aditya23043/split36/src/firmware/kmk_firmware-main/boards/rhymestone/README.md

# Rhymestone

rhymestone

The Rhymestone is 40-key ortholinear split keyboard. Originally the Rhymestone
was created to be sold alongside the Treadstone and used as either a Macro pad
or a 10-key numpad, hence the similar naming conventions. However; the
Rhymestone is also often used as a standalone split keyboard by people who
prefer a 5 column ortholinear layout.

Extensions enabled by default  
- [Layers](/docs/en/layers.md) Need more keys than switches? Use layers.
- [BLE_Split](/docs/en/split_keyboards.md) Connects halves without wires
- [HoldTap](/docs/en/holdtap.md) Allows mod keys to act as different keys when tapped.

Common Extensions
- [Split](/docs/en/split_keyboards.md) Connects halves using a wire
- [Power](/docs/en/power.md) Powersaving features for battery life

## Microcontroller support

Update this line in `kb.py` to any supported microcontroller in `kmk/quickpin/pro_micro`:

```python
from kmk.quickpin.pro_micro.boardsource_blok import pinout as pins
```
