aditya23043/split36/src/firmware/kmk_firmware-main/boards/zodiark/README.md

# Zodiark

Zodiark

A split keyboard with 5x7 including a thumb cluster, encoders on each side, per
key RGB, and 2x I2C headers per side, supporting 1.3"/.96" 128x64 OLEDs (the
1.3" is an SSH1106 OLED, .91" 128x32 OLEDs.

Hardware Availability: Pending Group Buy - [Discord Link](https://discord.gg/BCSbXwskVt)

Extensions enabled by default  
- [Split](/docs/split.md) Connects halves using a wire.
- [Layers](/docs/layers.md) Need more keys than switches? Use layers.
- [PEG_RGB](/docs/peg_rgb_matrix.md) Light it up!
- [Display](/docs/en/display.md) Show information on the mini OLED display
