aditya23043/split36/src/firmware/kmk_firmware-main/boards/boardsource/Lulu/README.md

# Lulu

Lulu

Based on the form factor of the Lily58, but with new features. The Lulu is a 58 key split keyboard design by Boardsource, featuring a 6x4 columnar stagger and 4 thumb cluster keys on each hand. The Lulu is a perfect choice for people who want to be on a split keyboard but still want to have a fairly standard amount of keys, and a premium case available.

Hardware Availability: [PCB & Case Source](https://boardsource.xyz/store/5ec9df84c6b834480de6c3d0)  
kb.py is designed to work with the PCBA version directly from them.

Extensions enabled by default  
- [Split](/docs/en/split.md) Connects halves using a wire.
- [Layers](/docs/en/layers.md) Need more keys than switches? Use layers.
- [PEG_RGB](/docs/en/peg_rgb_matrix.md) Light it up!
- [Display](/docs/en/display.md) Show information on the mini OLED display

Common Extensions
- [Power](/docs/en/power.md) Powersaving features for battery life.
- [BLE_Split](/docs/en/split.md) Connects halves without wires (For the DIY version)
