aditya23043/split36/src/firmware/kmk_firmware-main/boards/boardsource/microdox/README.md

# Microdox

microdox

The Microdox is is a feature-packed 30% split columnar staggered keyboard. Even
though the Microdox is an extremely small keyboard it offers tons of features
from larger boards while maintaining a tiny footprint.

Extensions enabled by default  
- [Layers](/docs/en/layers.md) Need more keys than switches? Use layers.
- [BLE_Split](/docs/en/split_keyboards.md) Connects halves without wires
- [HoldTap](/docs/en/holdtap.md) Allows mod keys to act as different keys when tapped.

Common Extensions
- [Split](/docs/en/split_keyboards.md) Connects halves using a wire
- [Power](/docs/enpower.md) Powersaving features for battery life

## Microcontroller support

Update this line in `kb.py` to any supported microcontroller in `kmk/quickpin/pro_micro`:

```python
from kmk.quickpin.pro_micro.boardsource_blok import pinout as pins
```
