aditya23043/split36/src/firmware/kmk_firmware-main/boards/gtips/reviung39/README.md

# Reviung39

Reviung39

Reviung39 is a 39 key keyboard designed by gtips. The Reviung39 sits somewhere
between an Atreus and a Corne, you get some nice ergonomic benefits based on its
quasi-split design and since a true split keyboard isn't for everyone, this is
an awesome middle ground. I find this keyboard extremely comfortable to use.

kb.py is designed to work with the nice!nano

Hardware Availability: [PCB & Case Data](https://github.com/gtips/reviung)

Extensions enabled by default
- [Layers](/docs/en/layers.md) Need more keys than switches? Use layers.
- [RGB](/docs/en/rgb.md) Light it up
- [HoldTap](/docs/en/holdtap.md) Allows mod keys to act as different keys when tapped.

## Microcontroller support

Update this line in `kb.py` to any supported microcontroller in `kmk/quickpin/pro_micro`:

```python
from kmk.quickpin.pro_micro.boardsource_blok import pinout as pins
```
