aditya23043/split36/imgs/2025-02-08_02-30.png

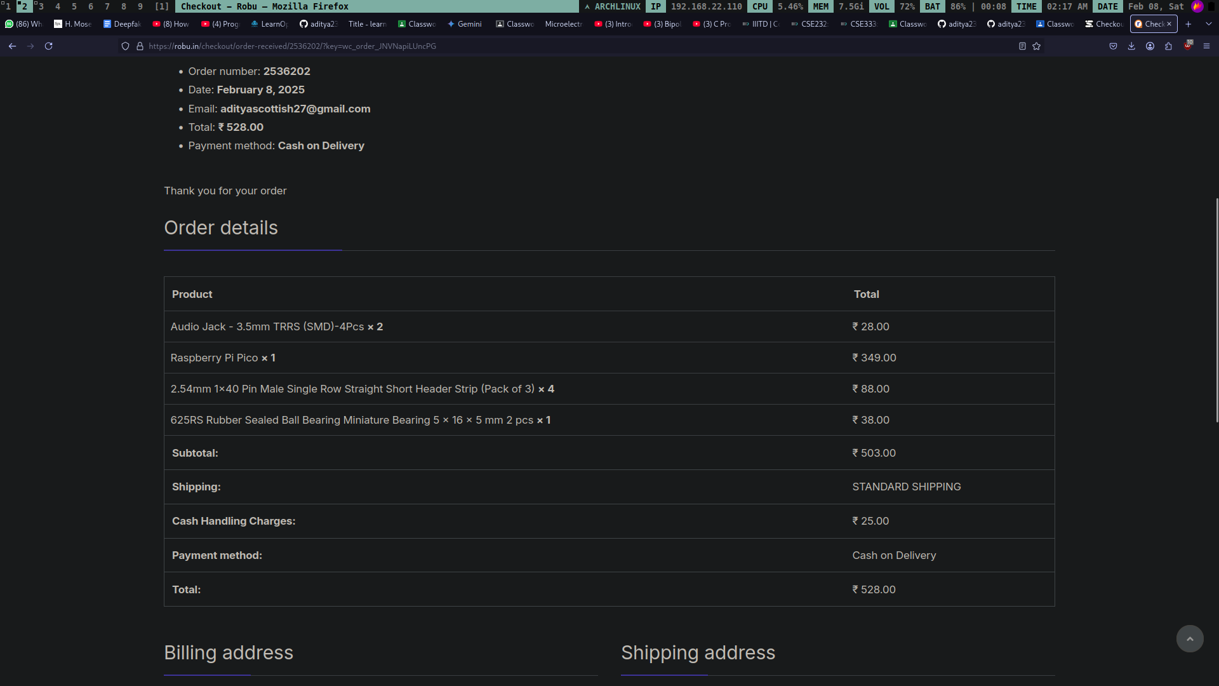
imgs/2025-02-08_02-30.png
