aditya23043/split36/imgs/2025-02-08_02-30_1.png

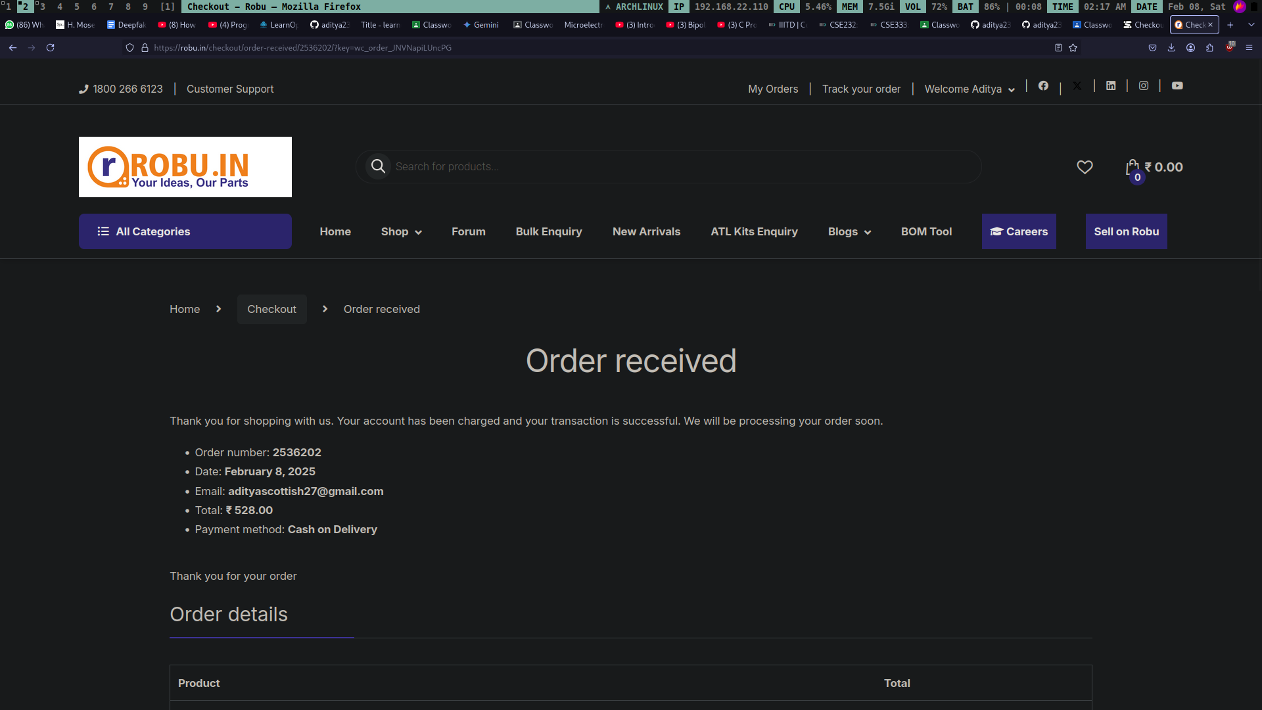
imgs/2025-02-08_02-30_1.png
