aditya23043/split36/imgs/2025-03-31_17-45.png

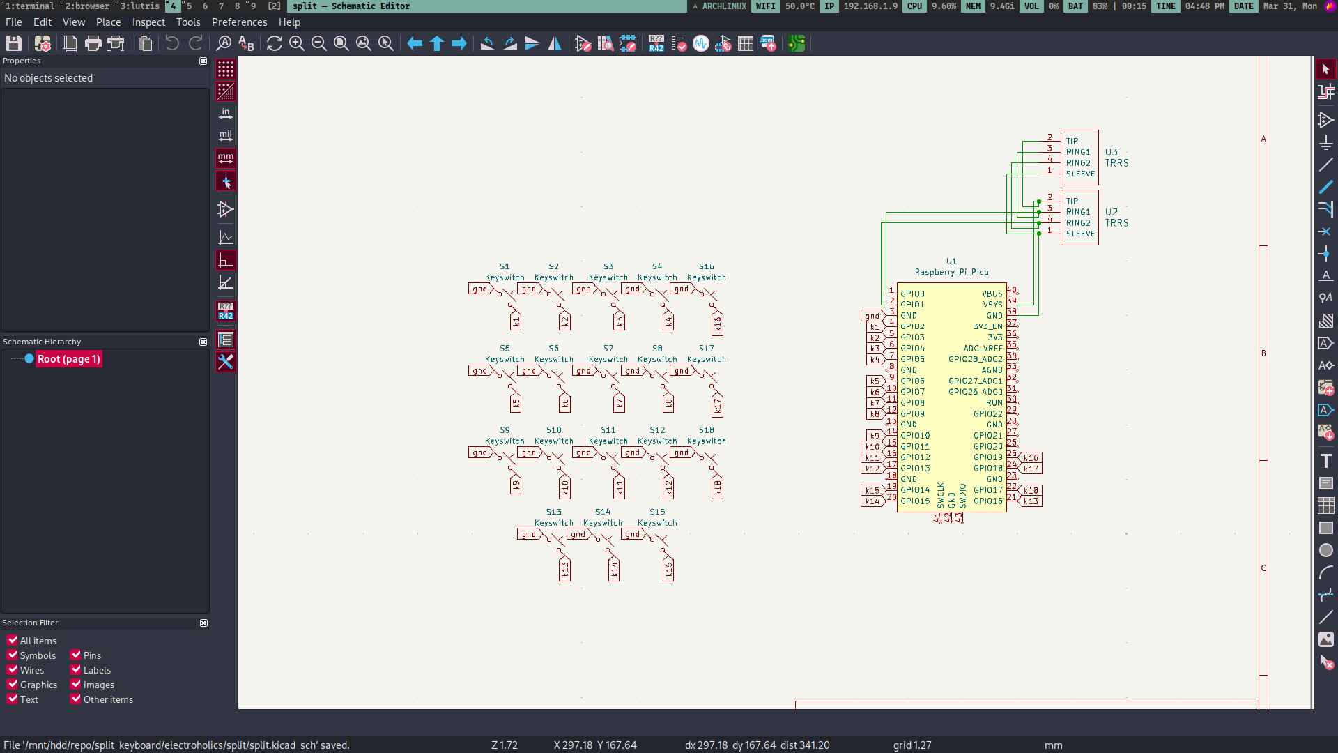
imgs/2025-03-31_17-45.png
