aditya23043/split36/imgs/2025-04-11_23-26.png

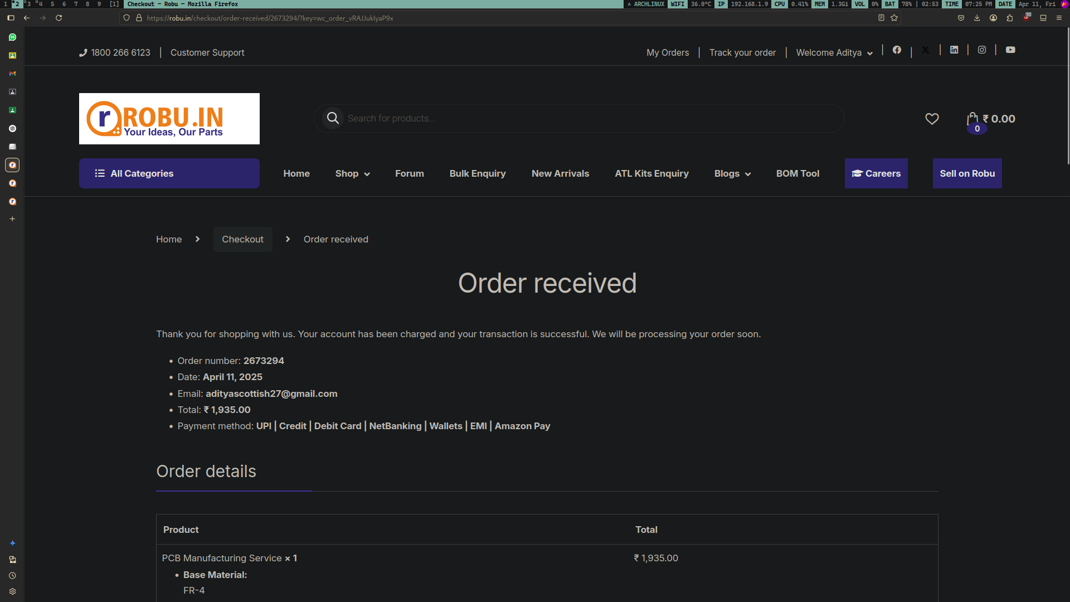
imgs/2025-04-11_23-26.png
