aditya23043/split36/imgs/dslr/IMG_3497.JPG

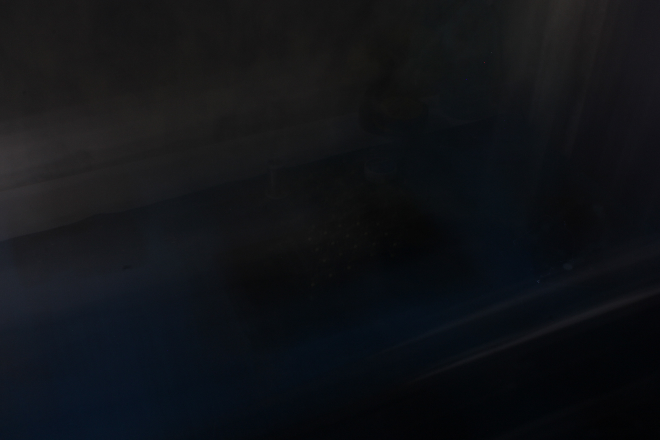
imgs/dslr/IMG_3497.JPG
