aditya23043/split36/imgs/dslr/IMG_3498.JPG

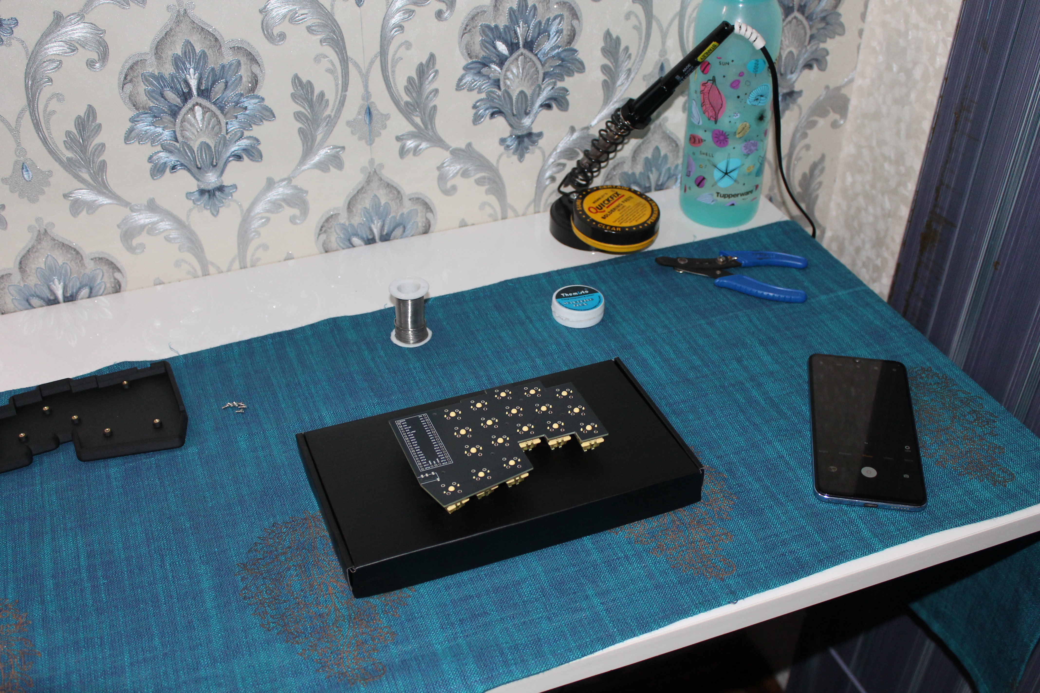
imgs/dslr/IMG_3498.JPG
