aditya23043/split36/imgs/dslr/IMG_3500.JPG

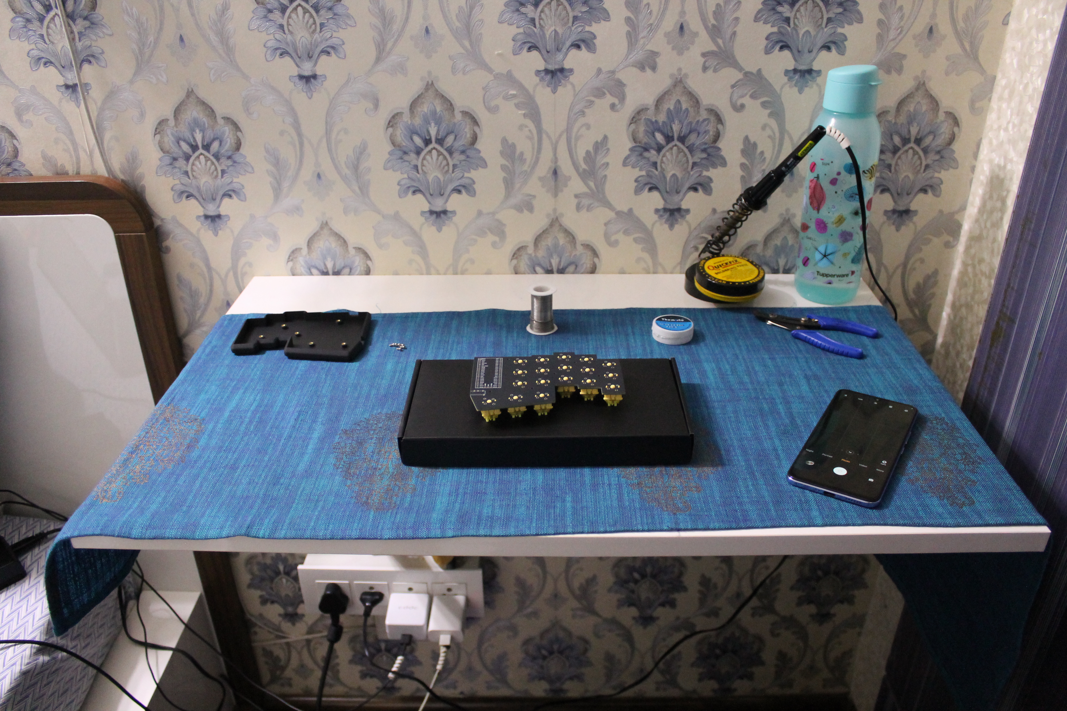
imgs/dslr/IMG_3500.JPG
