aditya23043/split36/imgs/dslr/IMG_3501.JPG

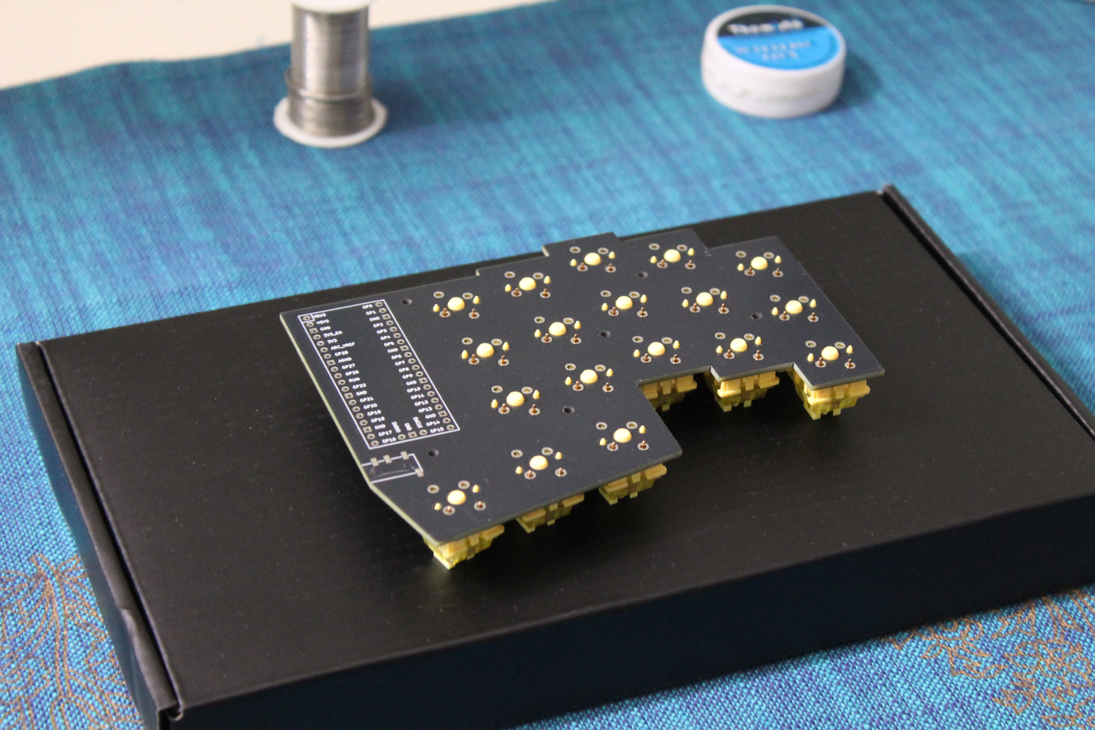
imgs/dslr/IMG_3501.JPG
