aditya23043/split36/imgs/dslr/IMG_3502.JPG

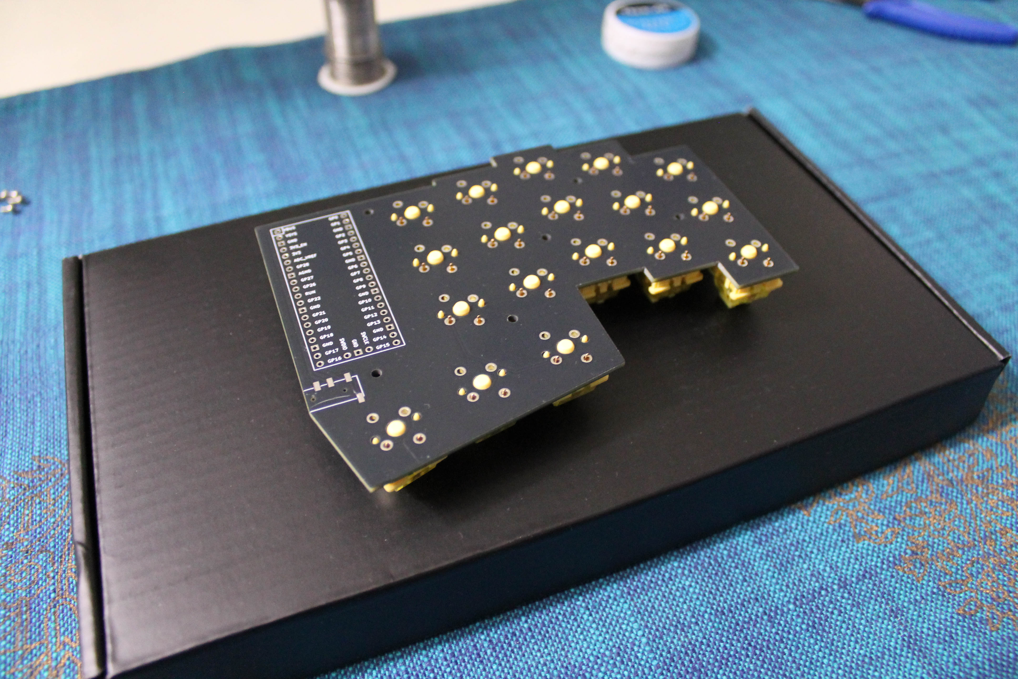
imgs/dslr/IMG_3502.JPG
