aditya23043/split36/imgs/dslr/IMG_3504.JPG

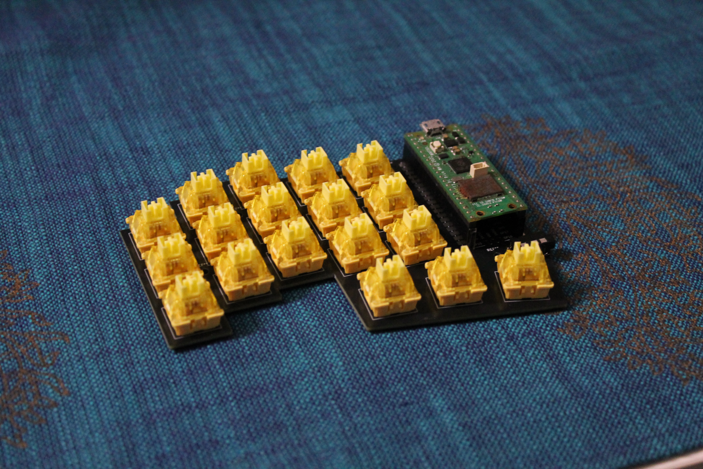
imgs/dslr/IMG_3504.JPG
