aditya23043/split36/imgs/dslr/IMG_3505.JPG

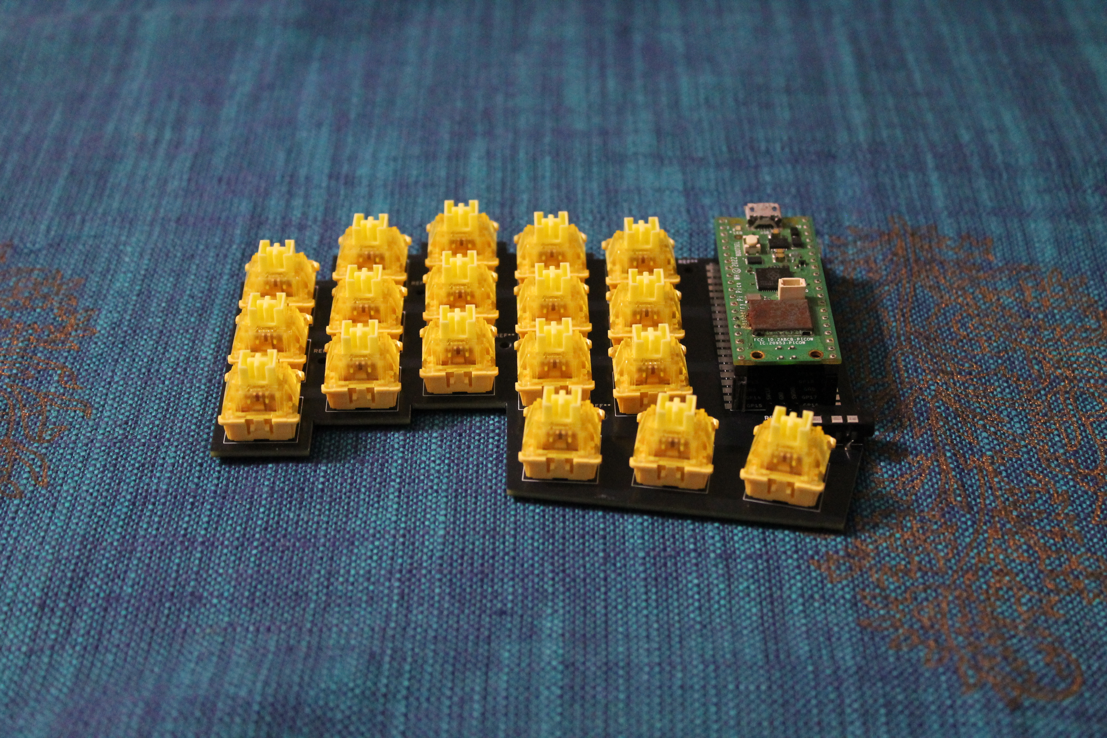
imgs/dslr/IMG_3505.JPG
