aditya23043/split36/imgs/dslr/IMG_3507.JPG

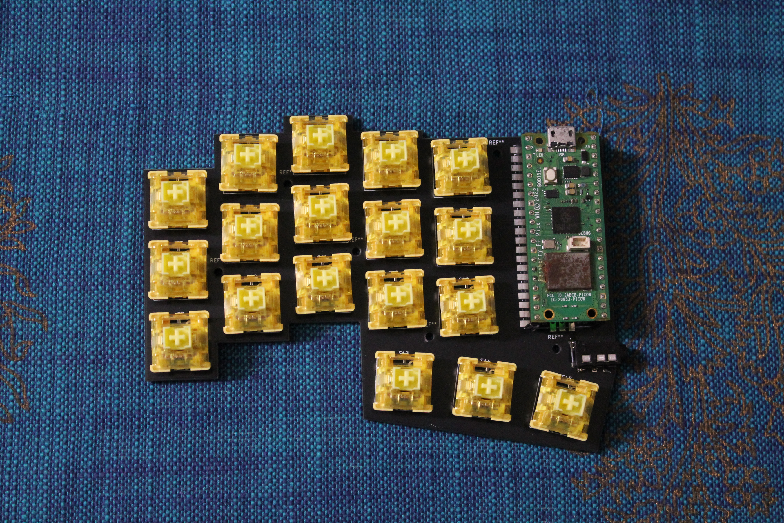
imgs/dslr/IMG_3507.JPG
