aditya23043/split36/imgs/dslr/IMG_3509.JPG

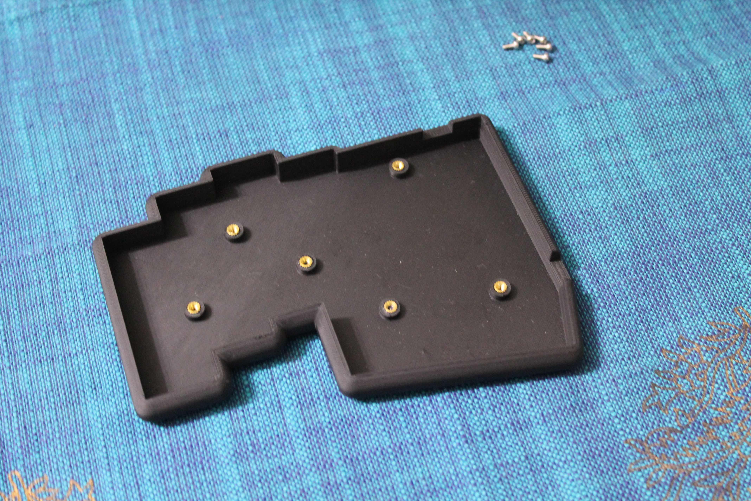
imgs/dslr/IMG_3509.JPG
