aditya23043/split36/imgs/dslr/IMG_3511.JPG

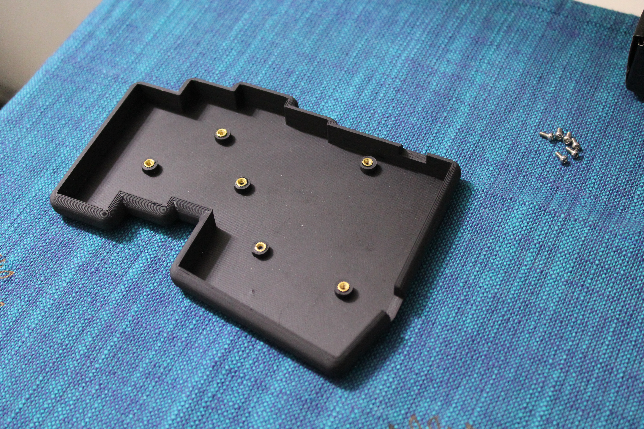
imgs/dslr/IMG_3511.JPG
