aditya23043/split36/imgs/dslr/IMG_3512.JPG

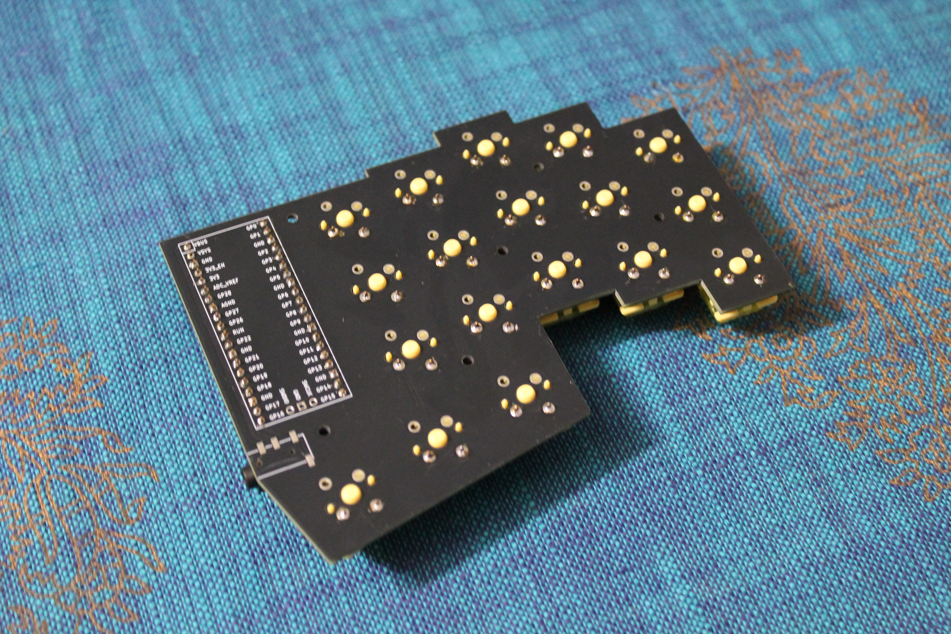
imgs/dslr/IMG_3512.JPG
