aditya23043/split36/imgs/dslr/IMG_3513.JPG

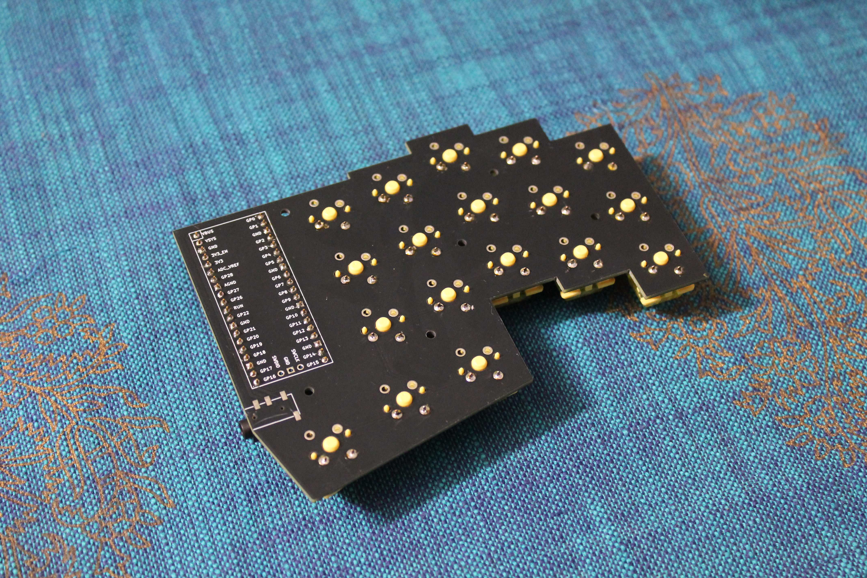
imgs/dslr/IMG_3513.JPG
