aditya23043/split36/imgs/dslr/IMG_3515.JPG

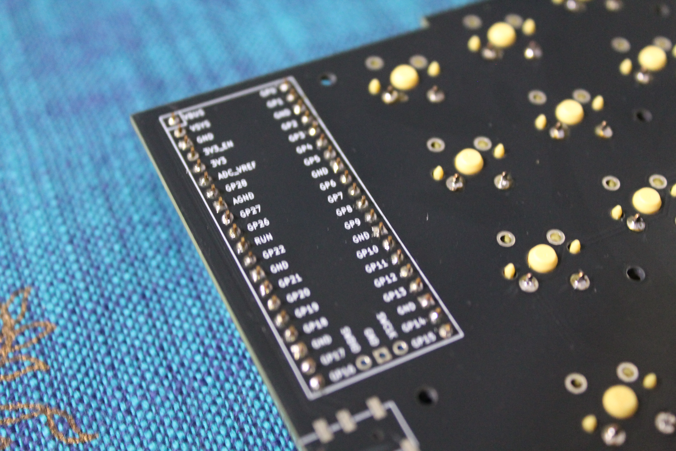
imgs/dslr/IMG_3515.JPG
