aditya23043/split36/imgs/dslr/IMG_3516.JPG

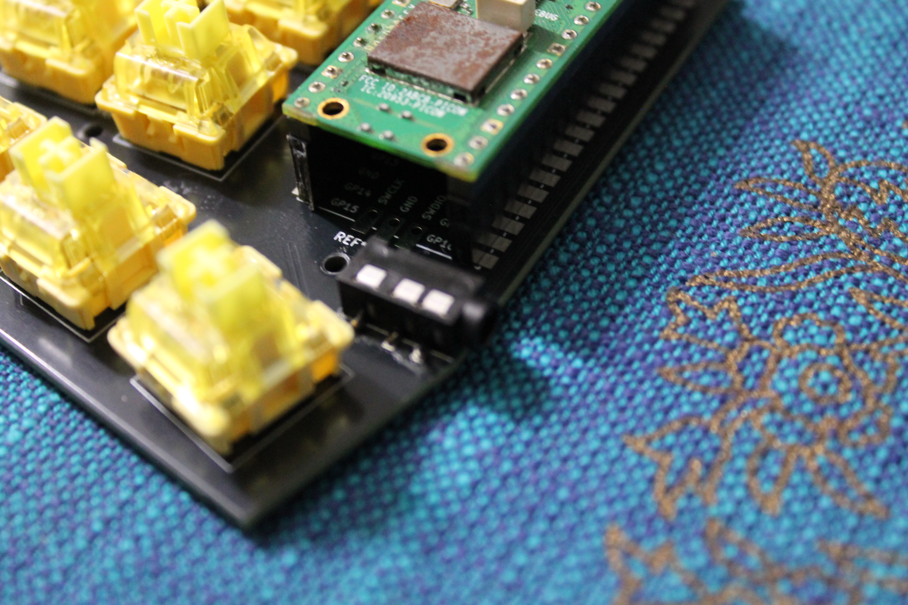
imgs/dslr/IMG_3516.JPG
