aditya23043/split36/imgs/dslr/IMG_3520.JPG

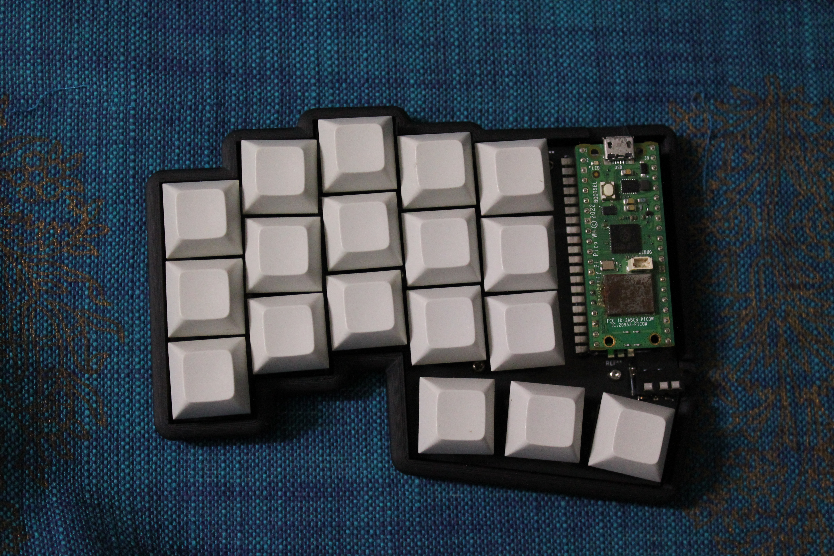
imgs/dslr/IMG_3520.JPG
