aditya23043/split36/imgs/dslr/IMG_34971.png

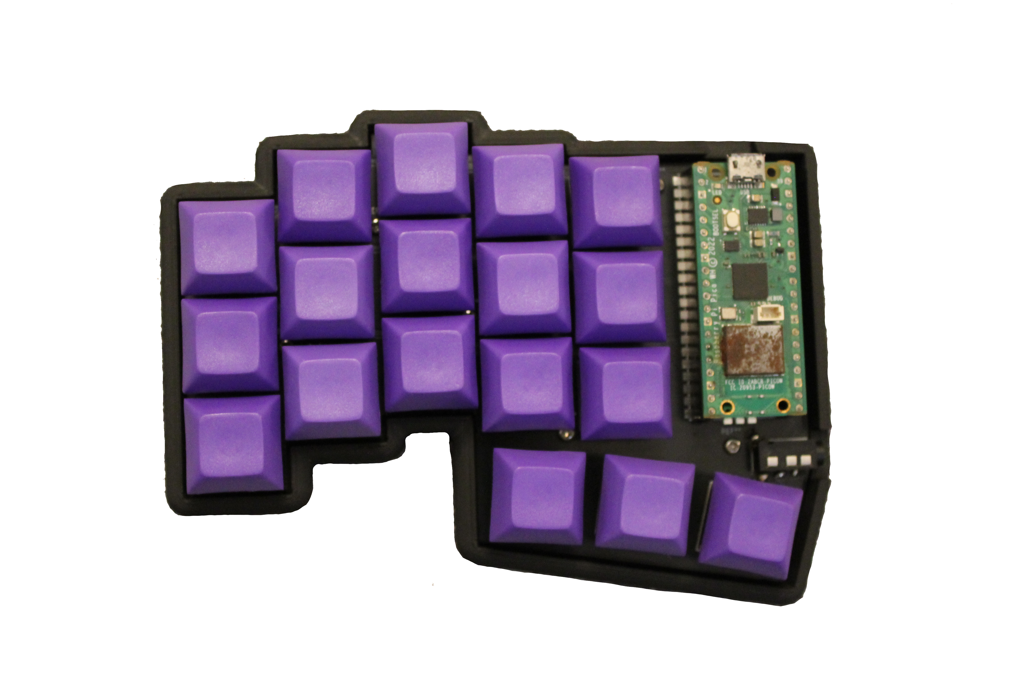
imgs/dslr/IMG_34971.png
