aditya23043/split36/imgs/mx.jpg

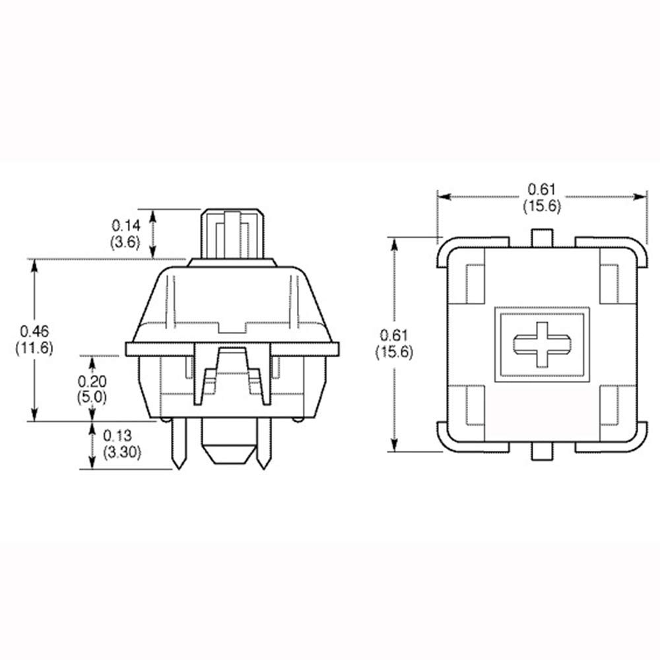
imgs/mx.jpg
