aditya23043/split36/imgs/MXswitches3.png

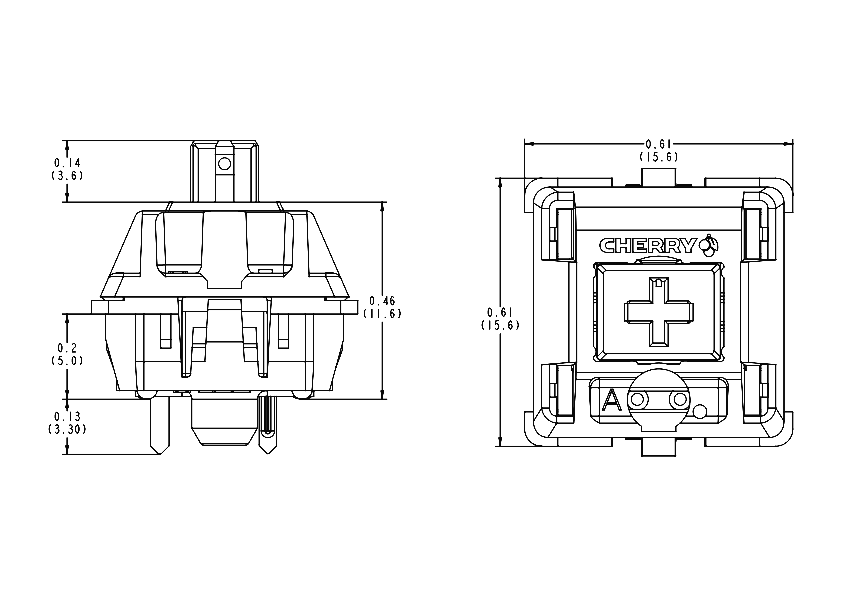
imgs/MXswitches3.png
