aditya23043/split36/imgs/WhatsApp Image 2025-05-03 at 23.23.30.jpeg

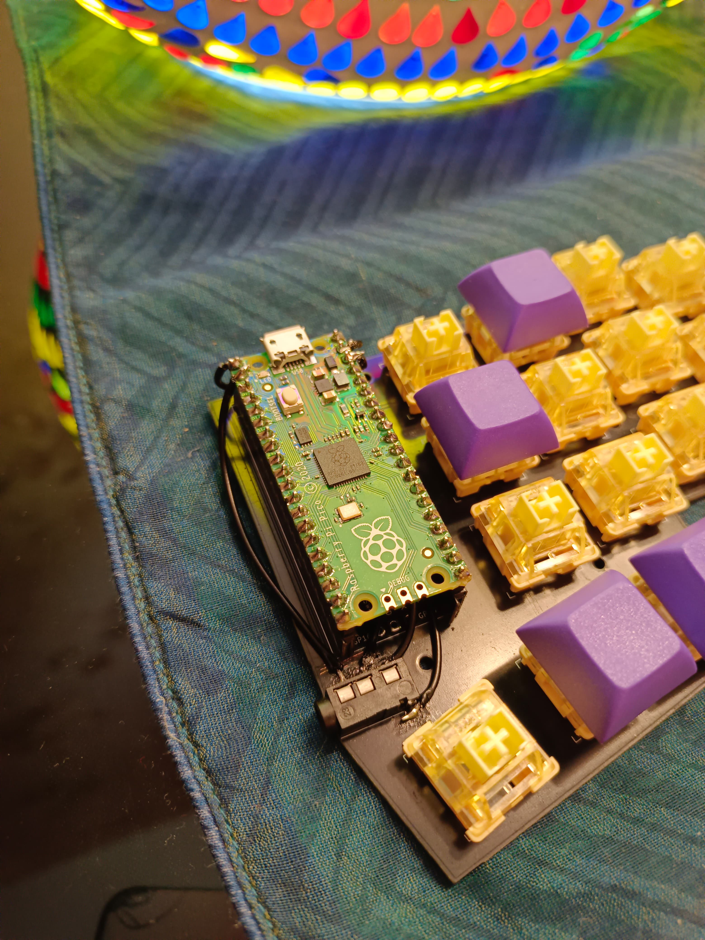
imgs/WhatsApp Image 2025-05-03 at 23.23.30.jpeg
