aditya23043/split36/pcb/split-B_Cu.dxf

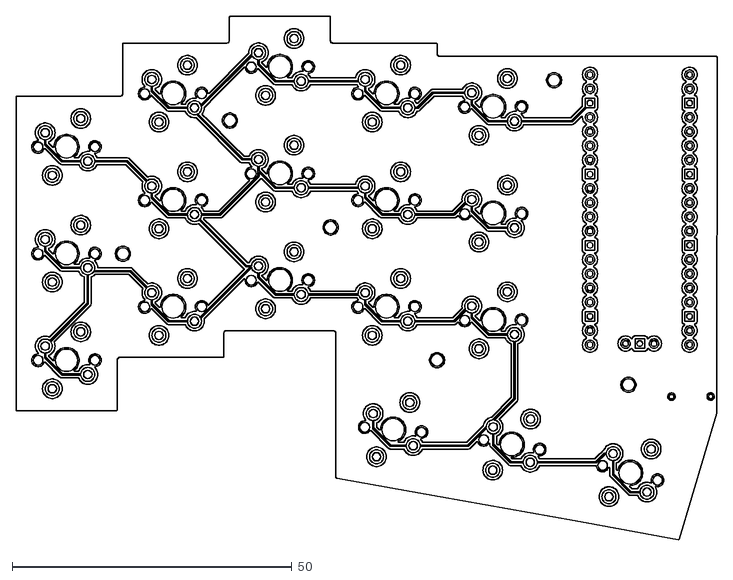
[picture p70: CAD file, 2025-04-11]
pcb/split-B_Cu.dxf
125.2 x 93.4
