aditya23043/split36/pcb/pcb.dxf

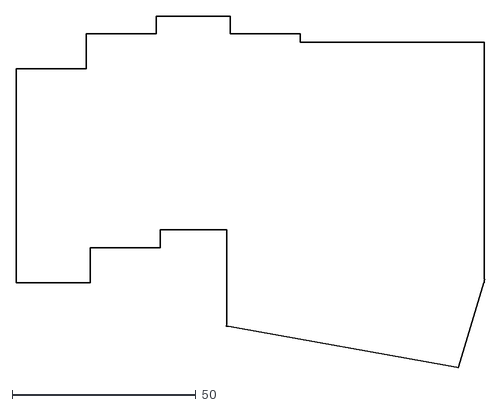
[picture p71: CAD file, 2025-04-11]
pcb/pcb.dxf
127.3 x 95.6
