aditya23043/split36/pcb/split-F_Cu.dxf

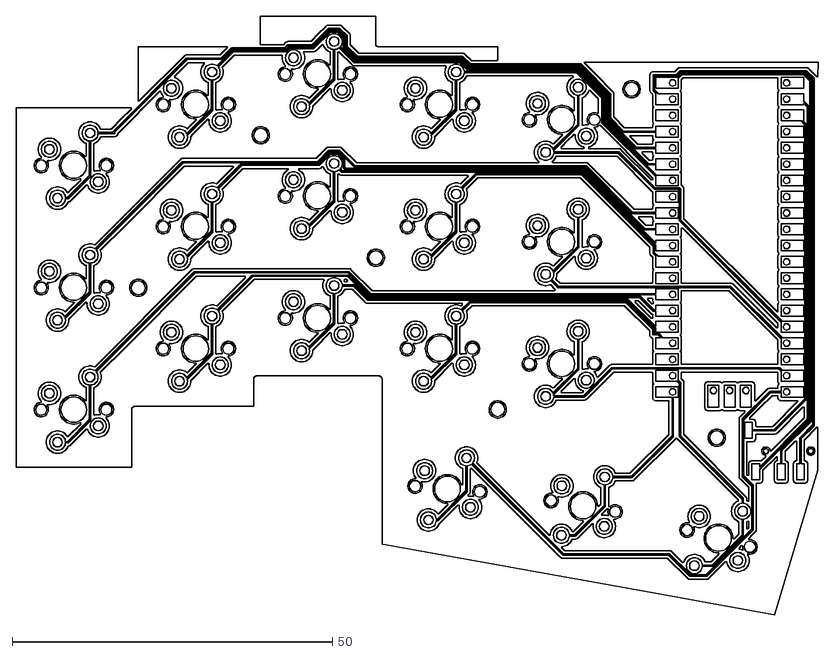
[picture p72: CAD file, 2025-04-11]
pcb/split-F_Cu.dxf
125.2 x 93.4
