aditya23043/split36/imgs/dslr/IMG_3522.JPG

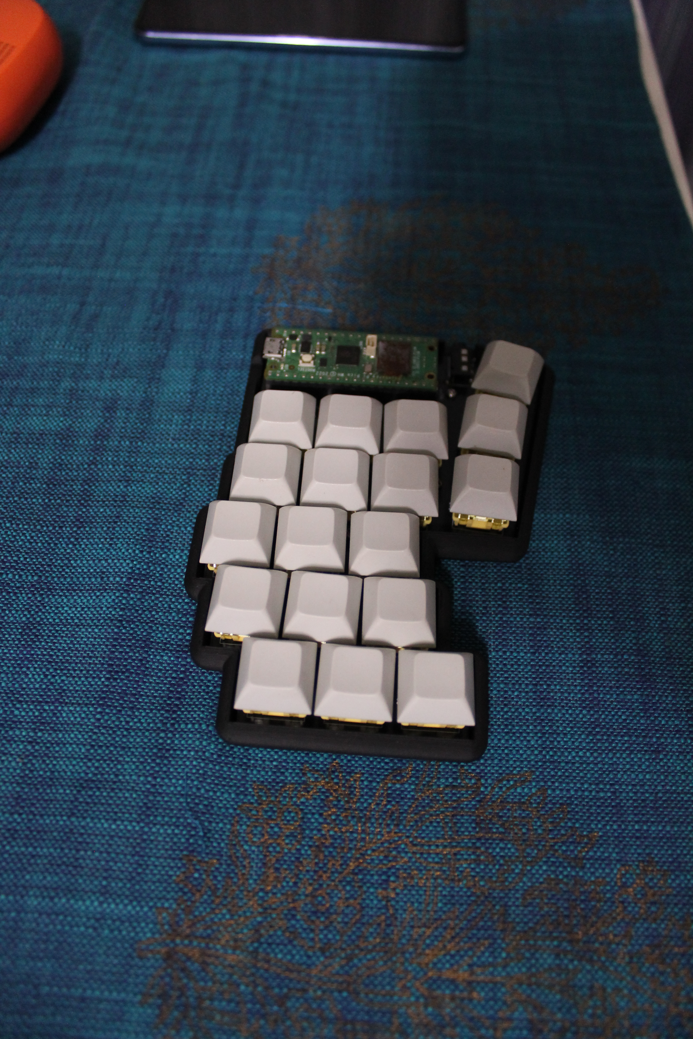
imgs/dslr/IMG_3522.JPG
